rksdna/fc100/software/MainWindow.h

#ifndef MAINWINDOW_H
#define MAINWINDOW_H

#include <QMainWindow>

class Device;

class MainWindow : public QMainWindow
{
    Q_OBJECT
public:
    explicit MainWindow(QWidget *parent = 0);

protected:
    void closeEvent(QCloseEvent *event);

private:
    void preferences();
    void saveAs();
    void about();

public:
    Device * const m_device;
};

#endif // MAINWINDOW_H
