rksdna/fc100/firmware/fc100/include/counter.h

/*
 * Reciprocal counter USB bridge
 * Copyright (c) 2018 rksdna, murych
 *
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
 * THE SOFTWARE IS PROVIDED "AS IS", WITHOUT WARRANTY OF ANY KIND, EXPRESS OR
 * IMPLIED, INCLUDING BUT NOT LIMITED TO THE WARRANTIES OF MERCHANTABILITY,
 * FITNESS FOR A PARTICULAR PURPOSE AND NONINFRINGEMENT. IN NO EVENT SHALL THE
 * AUTHORS OR COPYRIGHT HOLDERS BE LIABLE FOR ANY CLAIM, DAMAGES OR OTHER
 * LIABILITY, WHETHER IN AN ACTION OF CONTRACT, TORT OR OTHERWISE, ARISING FROM,
 * OUT OF OR IN CONNECTION WITH THE SOFTWARE OR THE USE OR OTHER DEALINGS IN
 * THE SOFTWARE.
 */

#ifndef COUNTER
#define COUNTER

#include <types.h>

struct counter
{
    u8_t dac1;
    u8_t dac2;
    u8_t mode;
    u8_t ctrl;
    u8_t id;
    u8_t ack;
    u8_t tac_strt;
    u8_t tac_stop;
    u32_t cnt;
    u32_t tmr;
};

#define COUNTER_DAC1 ((u8_t)0x00)
#define COUNTER_DAC2 ((u8_t)0x01)
#define COUNTER_MODE ((u8_t)0x02)
#define COUNTER_CTRL ((u8_t)0x03)
#define COUNTER_ID ((u8_t)0x04)
#define COUNTER_ACK ((u8_t)0x05)
#define COUNTER_TAC_START ((u8_t)0x06)
#define COUNTER_TAC_STOP ((u8_t)0x07)
#define COUNTER_CNT ((u8_t)0x08)
#define COUNTER_TMR ((u8_t)0x0C)

#define COUNTER_DAC_DAC ((u8_t)0xFF)

#define COUNTER_MODE_STRT ((u8_t)0x03)
#define COUNTER_MODE_STRT_0 ((u8_t)0x01)
#define COUNTER_MODE_STRT_1 ((u8_t)0x02)
#define COUNTER_MODE_STRT_CH1R ((u8_t)0x00)
#define COUNTER_MODE_STRT_CH1F ((u8_t)0x01)
#define COUNTER_MODE_STRT_CH2R ((u8_t)0x02)
#define COUNTER_MODE_STRT_CH2F ((u8_t)0x03)
#define COUNTER_MODE_STRT_BITS(x) ((u8_t)(x) & COUNTER_MODE_STRT)

#define COUNTER_MODE_STOP ((u8_t)0x0C)
#define COUNTER_MODE_STOP_0 ((u8_t)0x04)
#define COUNTER_MODE_STOP_1 ((u8_t)0x08)
#define COUNTER_MODE_STOP_CH1R ((u8_t)0x00)
#define COUNTER_MODE_STOP_CH1F ((u8_t)0x04)
#define COUNTER_MODE_STOP_CH2R ((u8_t)0x08)
#define COUNTER_MODE_STOP_CH2F ((u8_t)0x0C)
#define COUNTER_MODE_STOP_BITS(x) (((u8_t)(x) << 2) & COUNTER_MODE_STOP)

#define COUNTER_MODE_CNT ((u8_t)0x30)
#define COUNTER_MODE_CNT_0 ((u8_t)0x10)
#define COUNTER_MODE_CNT_1 ((u8_t)0x20)
#define COUNTER_MODE_CNT_CH1R ((u8_t)0x00)
#define COUNTER_MODE_CNT_CH1F ((u8_t)0x10)
#define COUNTER_MODE_CNT_CH2R ((u8_t)0x20)
#define COUNTER_MODE_CNT_CH2F ((u8_t)0x30)
#define COUNTER_MODE_CNT_BITS(x) (((u8_t)(x) << 4) & COUNTER_MODE_CNT)

#define COUNTER_MODE_TMR ((u8_t)0x40)
#define COUNTER_MODE_TMR_CLK ((u8_t)0x00)
#define COUNTER_MODE_TMR_REF ((u8_t)0x40)
#define COUNTER_MODE_TMR_BITS(x) (((u8_t)(x) << 6) & COUNTER_MODE_TMR)

#define COUNTER_MODE_CLR ((u8_t)0x80)

#define COUNTER_CTRL_STRT ((u8_t)0x01)
#define COUNTER_CTRL_STOP ((u8_t)0x02)
#define COUNTER_CTRL_CLB_ZS ((u8_t)0x04)
#define COUNTER_CTRL_CLB_FS ((u8_t)0x08)

#define COUNTER_CTRL_HPF_CH1 ((u8_t)0x10)
#define COUNTER_CTRL_HPF_CH1_BITS(x) (((u8_t)(x) << 4) & COUNTER_CTRL_HPF_CH1)

#define COUNTER_CTRL_HPF_CH2 ((u8_t)0x20)
#define COUNTER_CTRL_HPF_CH2_BITS(x) (((u8_t)(x) << 5) & COUNTER_CTRL_HPF_CH2)

#define COUNTER_CTRL_TEST ((u8_t)0x40)
#define COUNTER_CTRL_CLR ((u8_t)0x80)

#define COUNTER_TAC_TAC ((u8_t)0xFF)

#define COUNTER_ACK_STOP ((u8_t)0x01)
#define COUNTER_ACK_STRT ((u8_t)0x02)

#define COUNTER_ID_ID ((u8_t)0xFF)

#define COUNTER_CNT_CNT ((u32_t)0xFFFFFFFF)
#define COUNTER_TMR_TMR ((u32_t)0xFFFFFFFF)

#endif
