rksdna/fc100/software/PopupButton.h

#ifndef POPUPBUTTON_H
#define POPUPBUTTON_H

#include <QVariant>
#include <QToolButton>

class PopupButton : public QToolButton
{
    Q_OBJECT

public:
    explicit PopupButton(QWidget *parent = 0);

    void appendData(const QString &text, const QVariant &data);

    QVariant currentData() const;
    void setCurrentData(const QVariant &data);

signals:
    void currentDataChanged();

protected:
    virtual void paintEvent(QPaintEvent *event);

private:
    void onTriggered();

private:
    QVariant m_data;
};

#endif // POPUPBUTTON_H
