rksdna/fc100/software/ToolButton.h

#ifndef TOOLBUTTON_H
#define TOOLBUTTON_H

#include <QToolButton>

class ToolButton : public QToolButton
{
    Q_OBJECT

public:
    explicit ToolButton(QWidget *parent = 0);
};

#endif // TOOLBUTTON_H
